HenryLi-0/raven/updatelogs/logs202507/07092025.md

# 7/9/2025 - 15th Update!

wow today was quite the day, its already 10 PM..., anyways watched another movie today, time to start working! yeah so today in the doctors office i got bored while waiting and decided to research a couple of boost convertors (since the current MT3608 we have has a max amp of 2A, which is quite sad when we want to power motors). anyways, found [this one](https://www.aliexpress.us/item/3256805882203198.html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), but it requires an input voltage of 10-32V, which the battery doesnt exactly deliver. therefore, we continue hunting.

yeah so its been 22 minutes and im starting to think there arent any boost convertors around for this job. so uh, found [this](https://www.aliexpress.us/item/2255800011462620.html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) but its limited to 5A in its input, so yeah. im kinda getting desperate here.

ok who keeps breaking the internet router

so i just had an idea, yeah its not gonna work (it was to skip the boost convertor for the motor and just attach it raw, but we need more volts!) yeah its been 45 minutes now and i cant find a good one. ok its now 11:05 PM and im just gonna take a break, ive looked through way too many aliexpress offers today...

ok im back at 12:15 AM and im honestly very tired lol, but lets try to push through.

[here's](https://www.aliexpress.us/item/3256805855172022.html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) a thing for 2A battery protection (choose `2S 20A Balance` or something)

alright, lets just finish this research phase, im getting really tired

what did i just come across

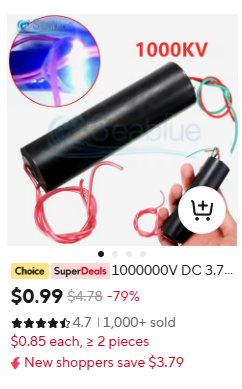
[picture p69: updatelogs/images/202507/07092025 - 1.png]
what this


ok theres actually no way i spent the entirety of today search for a single boost converter. anyways, im just gonna draw a wiring diagram real quick (yes for v3)

yeah so i just realized that... this soltuion kinda means that i need a step down to 5V thing for the motor system since we have a XIAO that doesnt want to become a frying pan

yeah ok, laid out all the components, its 1AM now, im just gonna wrap this up tomorrow (yay dont have to go outside tomorrow since its online on thursdays) (probably going to school on friday for driver practice? probably a good idea)

so yeah, thats it, good night!
