HenryLi-0/raven/updatelogs/logs202507/07062025.md

# 7/6/2025 - 12th Update!

yeah so we kinda gotta finish this...

just did a little research on the reviews of yesterday's overdischarge stuff, and it seems good! only downside is that its a *little* expensive (dont worry, welcome deal here! not sure how many deals i can get...) so, i guess we need to redraw the wiring diagram! (its 9:30 PM right now) wait a second, why does it say supply voltage 12V to 36V, guess this isnt the product for that!

so we need the entire battery output, but overdischarge protection to stop lower battery sus activity, so the battery should be able to deliver its stated 20A, but not get restrictied by the TP4056's 1A dishcharge thing (which is also one reason we arent including it on the spining bit now)

ok i gotta go for a second (its 10 right now), since my cousin is currently doing something in texas (i have no clue whats going on) ok three minutes later, and i guess they just diappeared off the face of the earth? i dont really know, gonna go back to search on aliexpress and LCSC, oh looks like theyre back

also the MT3608 that we had earlier does 2A max, which isnt enough... however, heres a [battery charger protection thing](https://www.aliexpress.us/item/3256807120302984.html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) (choose 2S 20A Balanced)! (uh idk if running this on only one battery would work?) yeah idk if this is the move, its layout looks super cursed, and im not exactly sure buying 4 batteries is the move. looking into making my own overdischarge protection circuit (bad idea), and i see a minecraft comparator reference

theres no way im soldering that

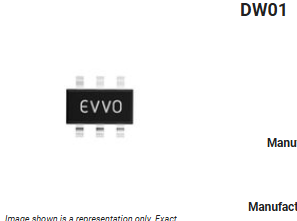
[picture p73: updatelogs/images/202507/07062025 - 1.png]
what the


anyways, heres some things i found:
- [1S 24A, might be the one! little sus, but should be good](https://www.aliexpress.us/item/3256805852468677.html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)
- [1S 10A, ok, less sus, but not enough amps!](https://www.aliexpress.us/item/3256806617397129.html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)
- [some 18650 format battery holder of sorts](https://www.digikey.com/en/products/detail/keystone-electronics/1044/5057795)

ok anyways its 11PM and im off to watch frozen 2 for like the fifteenth time ok see ya

ok its 12:13 AM and i just finished reading all the FRC servers im in (lurking behavior), anyways back to aliexpress! the `1S 24A` one (the first link) seems pretty ok, a little sketchy (not too many reviews) and one picture has a chip without a part marking in the photo, but reviews seem alright and the pictures. also, just realized, these will take a LONG time to ship. like it says july 19-22. eh, i guess trade off for being so cheap.

ok, so thats good! time to hunt LCSC for an A3144 and the MOSFET

hmm you need to by 5 A3144 at once, but i guess LCSC is better since its like $4 on aliexpress for also 5 (also, LCSC is probably more reputable) [here's](https://lcsc.com/product-detail/Hall-Switches_JSMSEMI-A3144EUA-T-JSM_C18188954.html?s_z=n_a3144) the link! also, whys the datasheet only in chinese

also, AP scores dont appear out yet? guess ill check in the morning

ok, since the pdf didnt allow copy pasting, i just downloaded it, went to google drive, uploaded it, and now i can copy and paste. yeah it just works like that. anyways, looks good! gonna hunt for the mosfet now, we also need leds...

yep, [here's](https://lcsc.com/product-detail/MOSFETs_STMicroelectronics-STP55NF06L_C77582.html?s_z=n_STP55NF06L) the STP55NF06L, cheaper than digikey!

ok, WS2812B now, shouldnt be too hard... oh yeah, nvm, since theres apparently 46 different ones, guess i spoke too soon... also thats crazy, 983885 and 1010610 leds in stock, how many do they mass produce at once?

waa who makes this many leds? (please send me your secret led stash)

leds leds leds

wait i need to find what footprint or at least what the LEDs i have look like... ok, whatever `LED_WS2812B_PLCC4_5.0x5.0mm_P3.2mm` means (probably 5mm by 5mm base and 3.2mm tall?) reading through [this datasheet](https://lcsc.com/datasheet/lcsc_datasheet_2506031657_XINGLIGHT-XL-5050RGBC-WS2812B_C2843785.pdf) for [these leds](https://lcsc.com/product-detail/RGB-LEDs-Built-in-IC_XINGLIGHT-XL-5050RGBC-WS2812B_C2843785.html?s_z=n_ws2812b) and dont really get whats 500 euros?

wha

wait this is funny

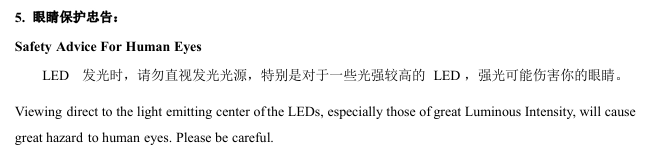
[picture p74: updatelogs/images/202507/07062025 - 4.png]
oops


anyways, im gonna continue research on the phone, currently 1:02 AM! (lots of things start tomorrow, guess i should try sleeping earlier today? probably not)
