HenryLi-0/raven/updatelogs/logs202506/06302025.md

# 6/30/2025 - 6th Update!

ok, nearing a week soon! today's CAD day! or more like tomorrow, since its actually 2 AM on 6/30/2025, and i just pushed the commit with the 6/29/2025 log (im a little too excited to work on this)

but since that's cad day, im actually gonna work on some of the firmware now! ok so its 2:37 AM now, and i got the theoretical settings and startup done, so now all the logic (predictive RPM and timing) needs to be done. gotta search this up, but hopefully it has decimal time tracking (as in, `time.time()` returns a decimal), since if it only returned whole numbers, that would make things a little less accurate!

ok, good night, see you tomorrow morning! (cad cad cad)

ok its 4:07 PM now, time to start CADing! gonna quickly export the kicad files into stl...

ok, everything imported (except that motor... do i just go hunting on aliexpress again?), lets get the CAD started! (its 4:25 PM now!) i guess we do a mastersketch (*DDS noises* (FRC reference))

ok so we need something heavy to keep the whole thing down ~~and not take off~~, so i guess we just make the top as light as possible (pocketing time) and the bottom have attachemts to put something like a weight on (or just make it heavy in general)

also turns out im actually designed it for M4 screws??? ok, wait, let me just take a break and think about this, since this CAD is not going the way i want it. what we want is a setup that looks like this:

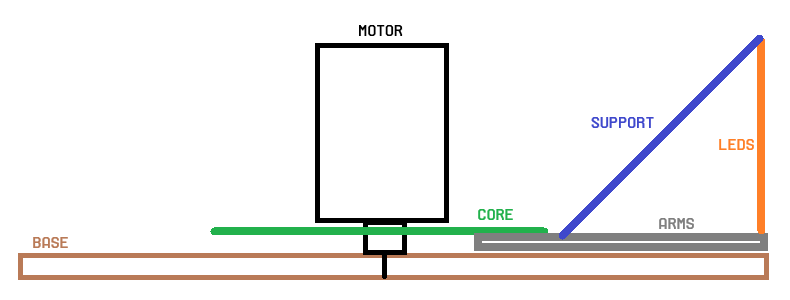
[picture p87: updatelogs/images/202506/06302025 - 1.png]
ms paint


and top down, something like (ok left at 5:05 PM and back at 11:20 PM!) (so uh kinda 6 hours passed and oopsie)

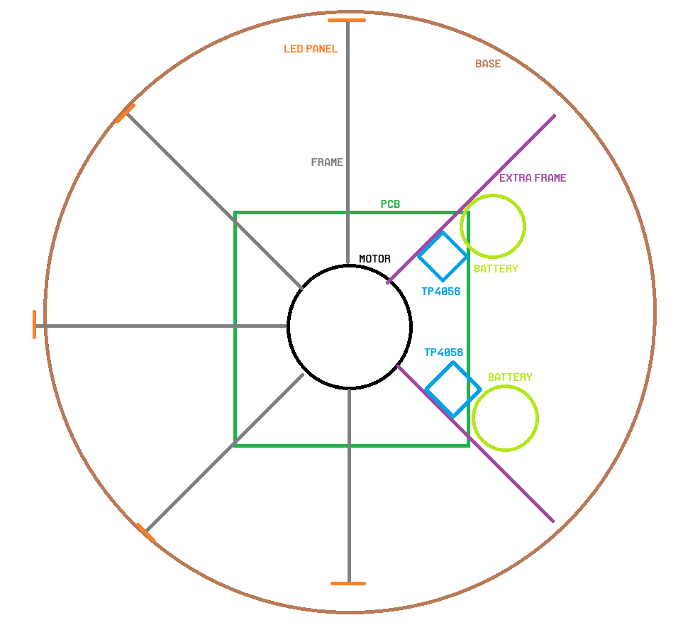
[picture p88: updatelogs/images/202506/06302025 - 2.png]
ms paint again


ignoring the fact that they are very not to scale, that's the general idea we're going for! gonna quickly take a visit to the bathroom, then we continue the CAD!

ok i need to figure out what motor im using, since i dont think using amazon shipping is gonna give the best prices (but, i really need to be careful of getting scammed on aliexpress lol) (mfw i say that and the second option is 3 motors prices at $0.99)

ok, so we need a shaft that isnt a perfect cylinder, or else we will not be able to get a grip... ok, so i actually cant find any non-sketchy D-shaft 775 motor, so i guess im gonna use [this one](https://www.aliexpress.us/item/3256807114067845.html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) that has a circular shaft, so ill probably use some hub or something (or just use superglue? idk)

hey, add [M4 screws (M4, 20mm)](https://www.aliexpress.us/item/3256804341271555.html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) to the BOM! and [these brass heat inserts (M4, OD 6mm, length 5mm)](https://www.aliexpress.us/item/3256803396040989.html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) while youre at it! and [these M4 nuts (M4)](https://www.aliexpress.us/item/3256807407546447.html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)! (ill have to look into this, but i *could* use the heat inserts as nuts... might be a bad idea, but ill look into it)

ok, gotta go to sleep now (its so early), but i do have a meeting tomorrow that i'll definitely not use to work on the CAD... no no, that would be such a terrible idea... who would ever do such thing? (*subtle foreshadowing*)

ok, just realized that the motor has some threaded m4 holes already! gotta update the PCB now, but heres the CAD so far!

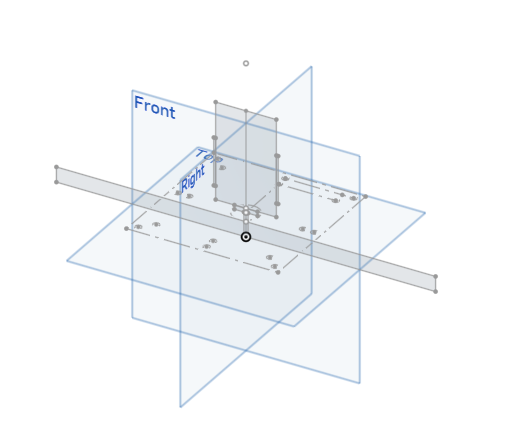
[picture p89: updatelogs/images/202506/06302025 - 3.png]
cad


ok good night now! (oops got caught being up at 12:40 AM oops)
