HenryLi-0/raven/updatelogs/logs202506/06262025.md

# 6/26/2025 - 2nd Update!

ok, so we're back! so, did a couple tests today...

**Test 1!**

firstly (sorry, this first one has no pictures), how fast do the LEDs have to flash before I can't see them changing? Turns out, around a wait time of `0.01` seconds was roughly the point where the colors seemed to start to seamlessly merge! Here's the example code:

```
import board
import neopixel
import time

led = board.D6
pixels = neopixel.NeoPixel(led, 9)
buffer = lambda ie: [ie for i in range(9)]

t = 0
while True:
    pixels[:] = buffer((255,0,0)) if t % 2 == 0 else buffer((0,0,255))
    t += 1
    time.sleep(0.01)
```

and after tuning the last line, we start to see purple! of course, the LEDs are still flashing the correct colors, as can be told by the fact that they are always red or blue when it "pauses" when you save firmware onto it. this means that, neopixels can, in fact, blend colors through pulsing colors faster than human detection! of course, we can't exactly test how fast they can update, but i do have an idea for later.

**Test 2!**

but now, a problem seems apparent. since we're spinning it round and round, for a certain period of time, one side does not recieve any light. basically, it acts sort of like PWM (you know, pulse width modulation), a strategy where "flickering" a device (such as an LED) is used to safely create an effect of percentage (so a half bright LED is powered 50% of the time). search it up, it'll explain better!

simply, we have to look at the effects of reduced light on the total brightness! of course, there is obviously an effect, but here's a comparison (LED flickering at max speed)

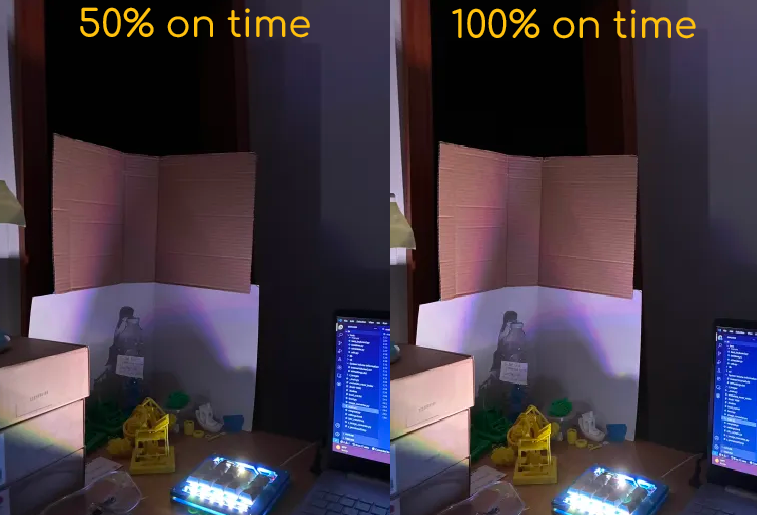
[picture p94: updatelogs/images/202506/06262025 - 1.png]
waw


no difference? try looking at the top right of each photo! the camera seems to catch the right photo with a bit more light! simply, the effect in person wasn't too much, it was noticably dimmer, but this shouldnt be an issue once we have nearly x5 the LEDs we currently have (49 outwards LEDs is crazy!)

and yeah, so interesting tests today! i'll be pretty busy tomorrow, but the plan is to find specifics (motor power, good motor speeds, battery stuff, etc.)! also, yes, i used my hackpad for this! ok, that's all for today, good night!
