HenryLi-0/raven/updatelogs/logs202508/08062025.md

# 8/6/2025 - 40th Update!

dealing 4 repositories of work at once isnt a good idea is it...

welcome back! todays just another quick update on the arrivals of stuff! today, LCSC packages came, two in fact! one containing a bunch of neat electronics, the other also containing neat electronics, except just one of them, that being the MOSFET! anyways, other than that, aliexpress has just told me that the package is now "at the local delivery center" and is about to take its final stretch to get here! luckily for me, i just happen to be able to stay home for the entirety of tomorrow!

at this very moment, in a repository far from here, a new repository rises to another YSWS! yep, planning on doing this one in 10 days, which is kinda insane. anyways, if we pull this off, it would be quite nice, except for the fact it kinda messes with my entire summer schedule. yeah, sorry ivo, gotta wait like two weeks...

anyways, thats about it! its just aliexpress and the PCBs, and we can get working! speaking of which, a quick update on JLCPCB, the package has also arrived at the same distribution facility, just one day shy of the LCSC ones! this means, hopefully, that it might come... tomorrow? we'll see! but for now, we wait for the local carrier on their way!

that's it folks! ok, yeah, got everything laid out on the table, hopefully we can begin assembly friday or this weekend! ok, good night!
