HenryLi-0/raven/PCB/repo.png

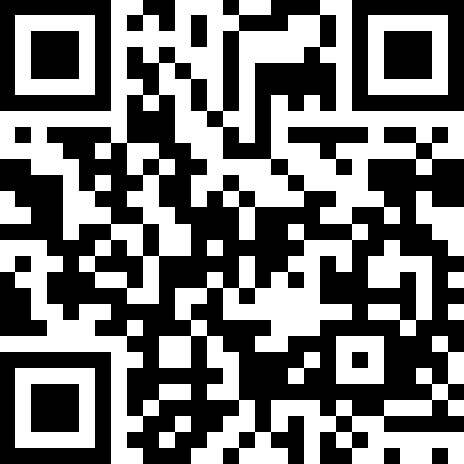
PCB/repo.png
