HenryLi-0/raven/PCB/vanity.png

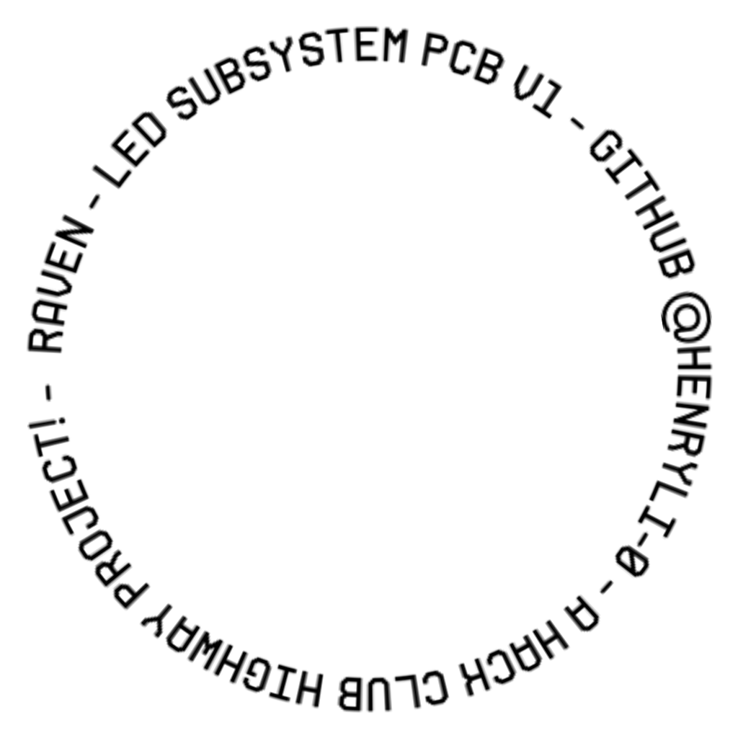
PCB/vanity.png
