HenryLi-0/raven/printing/motor top mount.step

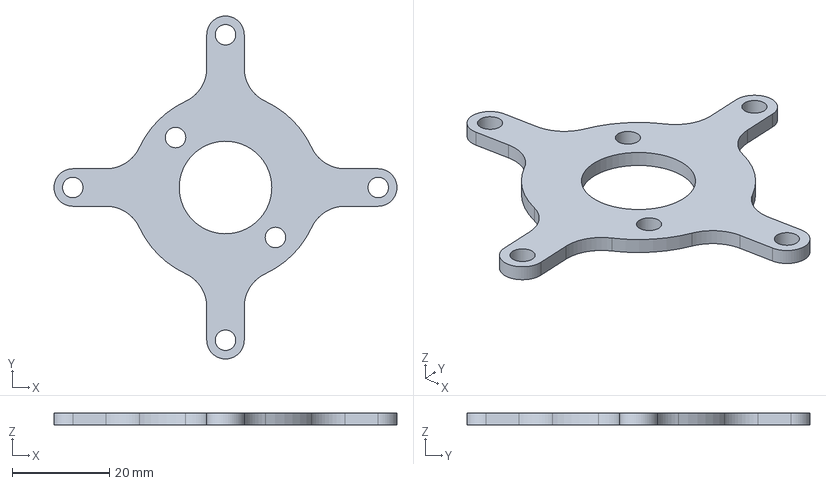
[picture p112: CAD file, 2025-08-12]
printing/motor top mount.step
70.4 x 70.4 x 2.50 mm
