HenryLi-0/raven/CAD/Arms/Raven-arm (diagonal)-2025-07-26 00-59-21.step

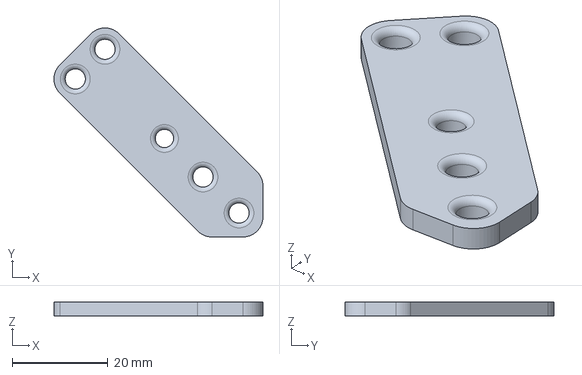
[picture p113: CAD file, 2025-07-26]
CAD/Arms/Raven-arm (diagonal)-2025-07-26 00-59-21.step
43.6 x 43.6 x 3.00 mm
