HenryLi-0/raven/CAD/Bracket/Raven-bracket ring-2025-07-26 00-59-33.step

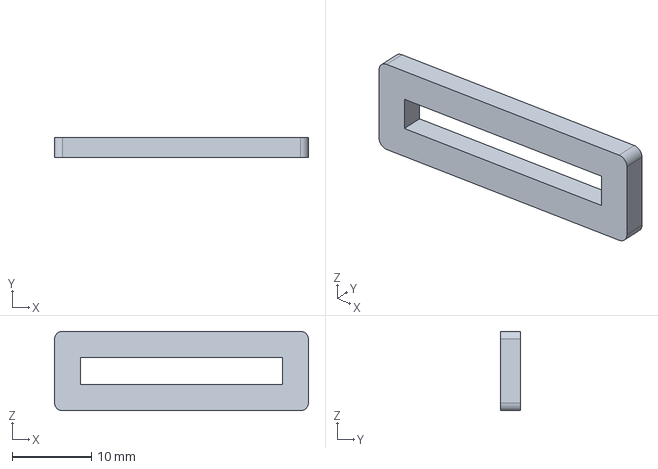
[picture p114: CAD file, 2025-07-26]
CAD/Bracket/Raven-bracket ring-2025-07-26 00-59-33.step
32.0 x 2.50 x 10.00 mm
