HenryLi-0/raven/CAD/Middle bits/Raven-motor top mount-2025-07-26 01-00-28.step

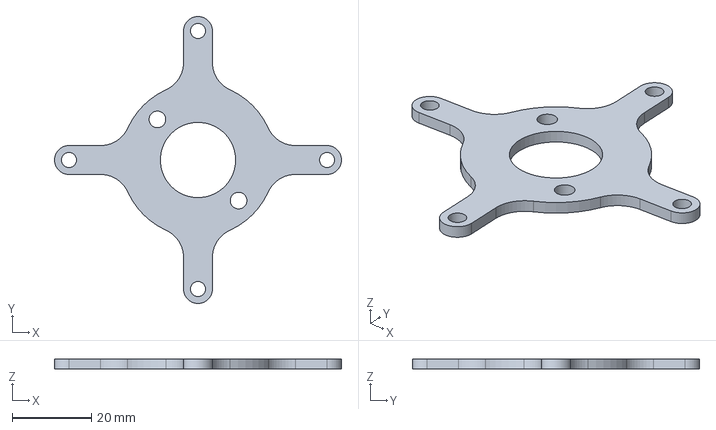
[picture p115: CAD file, 2025-07-26]
CAD/Middle bits/Raven-motor top mount-2025-07-26 01-00-28.step
72.5 x 72.5 x 2.50 mm
