HenryLi-0/raven/CAD/Motor bottom support/Raven-motor bottom mount-2025-07-26 01-00-34.step

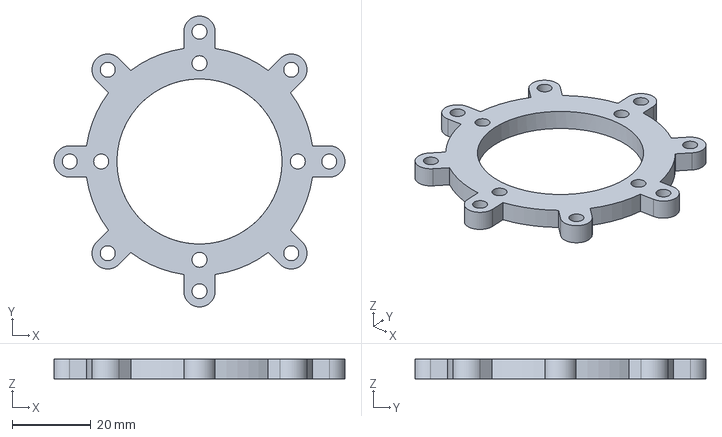
[picture p116: CAD file, 2025-07-26]
CAD/Motor bottom support/Raven-motor bottom mount-2025-07-26 01-00-34.step
74.0 x 74.0 x 5.00 mm
