HenryLi-0/raven/CAD/PCB representations/Raven-motor pcb-2025-07-26 01-02-24.step

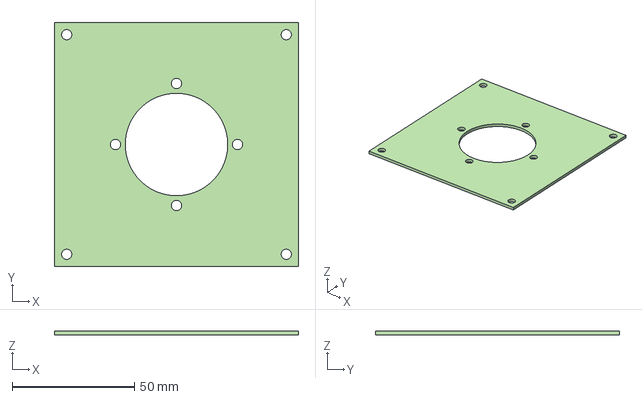
[picture p117: CAD file, 2025-07-26]
CAD/PCB representations/Raven-motor pcb-2025-07-26 01-02-24.step
100.0 x 100.0 x 1.60 mm
