HenryLi-0/raven/printing/3mf/electronics cover spacer x4.3mf

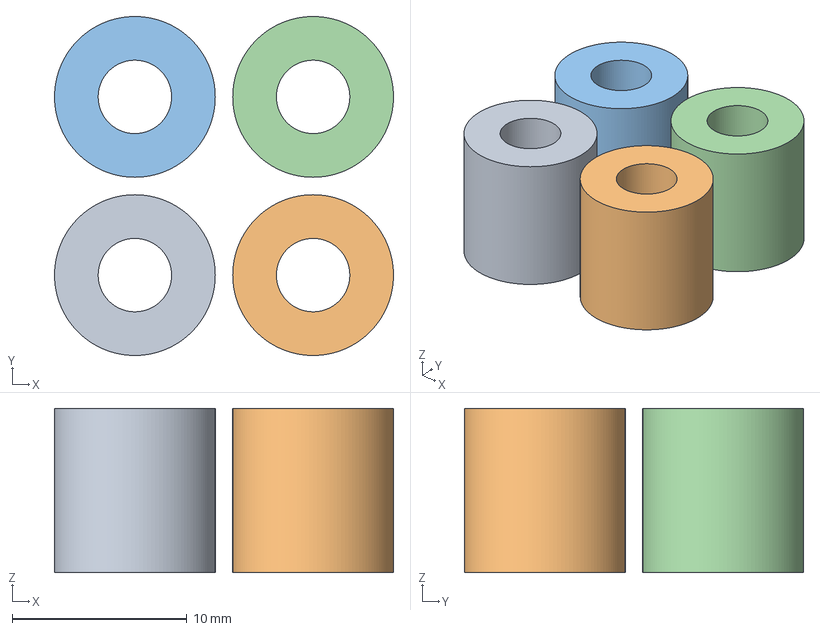
[picture p118: CAD file, 2025-08-08]
printing/3mf/electronics cover spacer x4.3mf
19.4 x 19.4 x 9.40 mm
electronics cover spacer.step x 4
