HenryLi-0/raven/CAD/Arms/Raven-inner spacer-2025-07-26 00-59-55.step

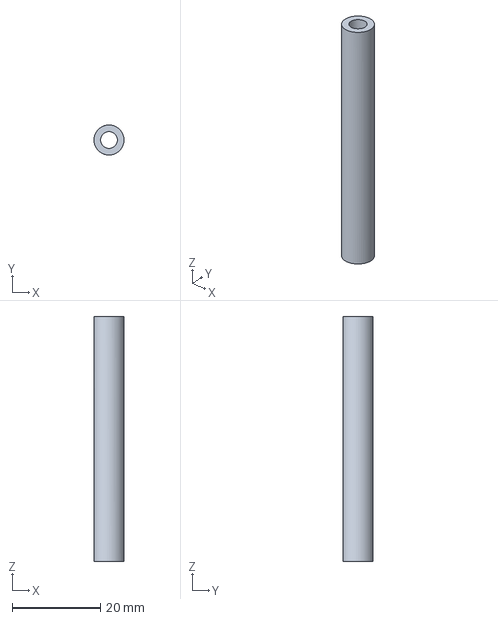
[picture p119: CAD file, 2025-07-26]
CAD/Arms/Raven-inner spacer-2025-07-26 00-59-55.step
6.80 x 6.80 x 55.4 mm
