HenryLi-0/raven/CAD/Bracket/Raven-bracket bracket-2025-07-26 00-59-29.step

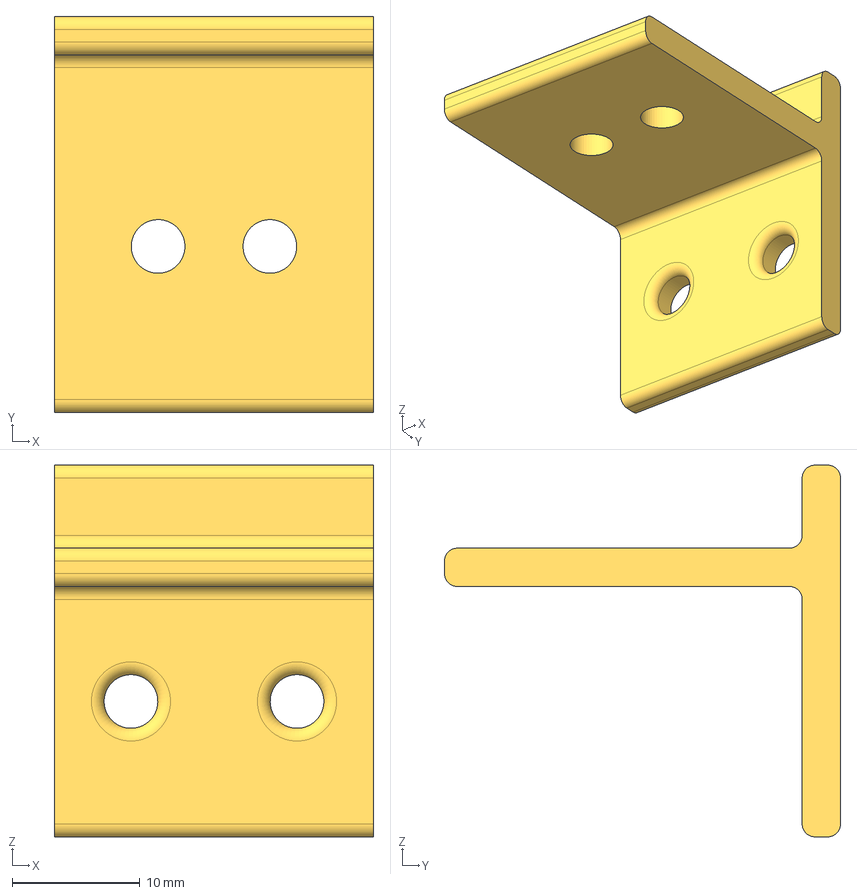
[picture p120: CAD file, 2025-07-26]
CAD/Bracket/Raven-bracket bracket-2025-07-26 00-59-29.step
25.0 x 31.0 x 29.1 mm
