HenryLi-0/raven/CAD/Motor bottom support/Raven-support leg straight-2025-07-26 01-00-44.step

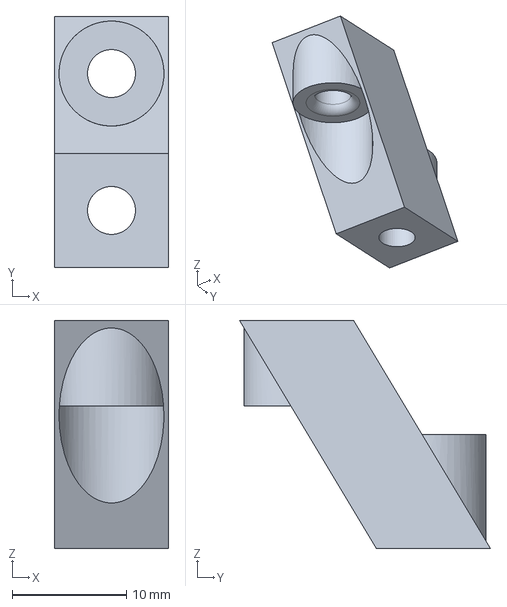
[picture p121: CAD file, 2025-07-26]
CAD/Motor bottom support/Raven-support leg straight-2025-07-26 01-00-44.step
10.0 x 22.0 x 20.0 mm
