HenryLi-0/raven/CAD/PCB representations/Raven-led panel-2025-07-26 01-02-17.step

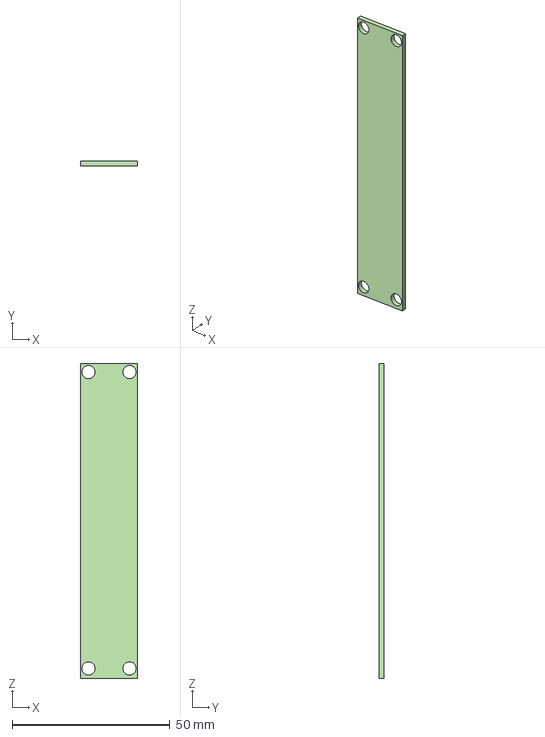
[picture p122: CAD file, 2025-07-26]
CAD/PCB representations/Raven-led panel-2025-07-26 01-02-17.step
18.0 x 1.60 x 99.9 mm
