HenryLi-0/raven/printing/3mf/support leg spacer x4.3mf

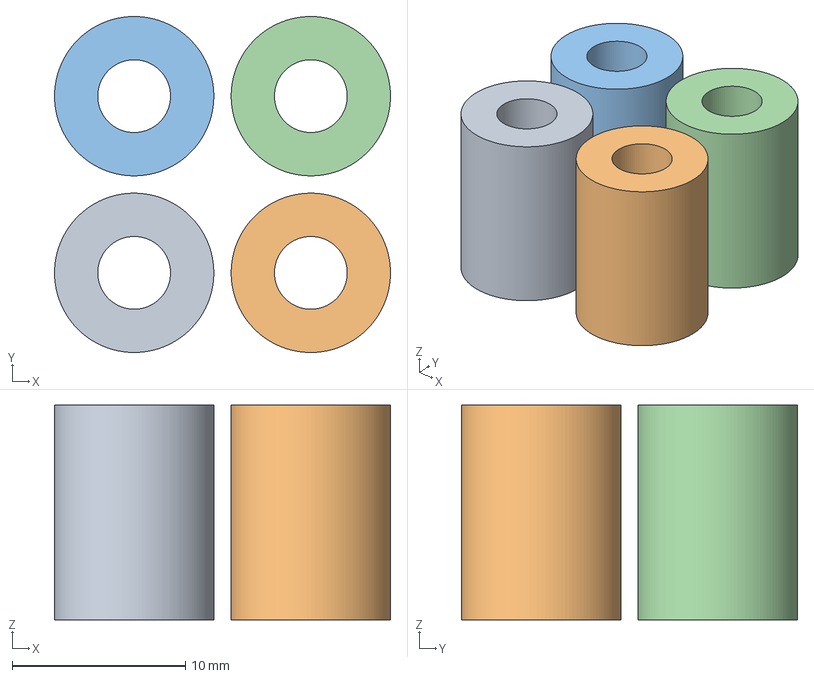
[picture p123: CAD file, 2025-08-08]
printing/3mf/support leg spacer x4.3mf
19.4 x 19.4 x 12.4 mm
support leg spacer.step x 4
