HenryLi-0/raven/printing/support leg spacer.step

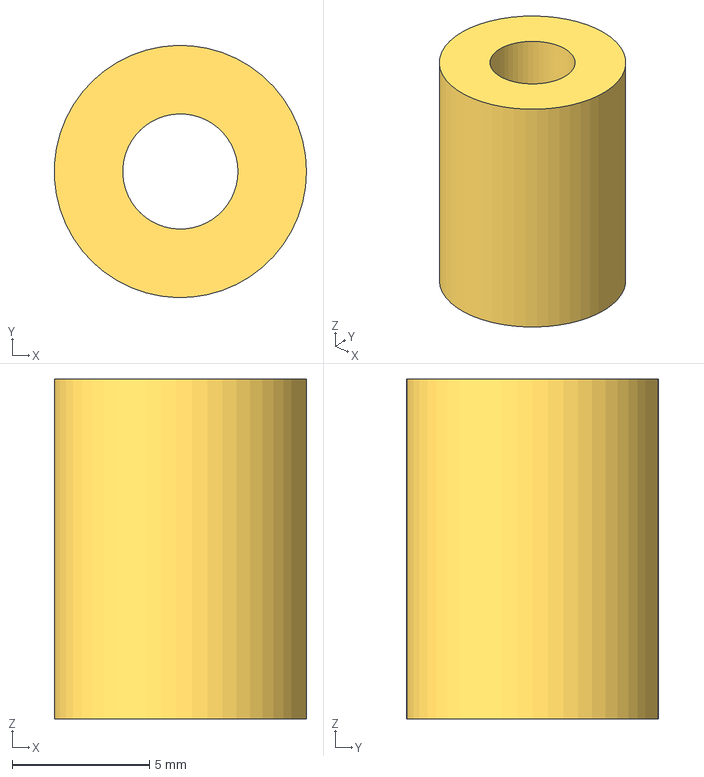
[picture p124: CAD file, 2025-08-08]
printing/support leg spacer.step
9.19 x 9.20 x 12.4 mm
