HenryLi-0/raven/CAD/Arms/Raven-arm (straight)-2025-07-26 00-59-16.step

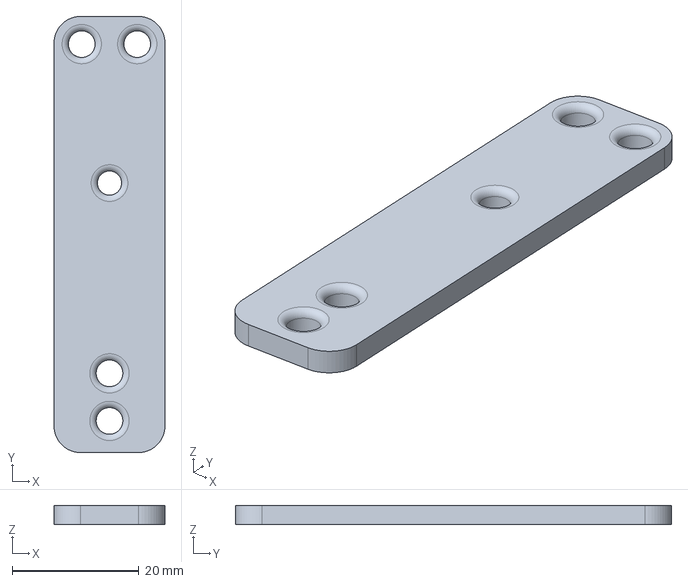
[picture p125: CAD file, 2025-07-26]
CAD/Arms/Raven-arm (straight)-2025-07-26 00-59-16.step
17.5 x 68.8 x 3.00 mm
