HenryLi-0/raven/CAD/Motor bottom support/Raven-motor bottom spacer-2025-07-26 01-00-40.step

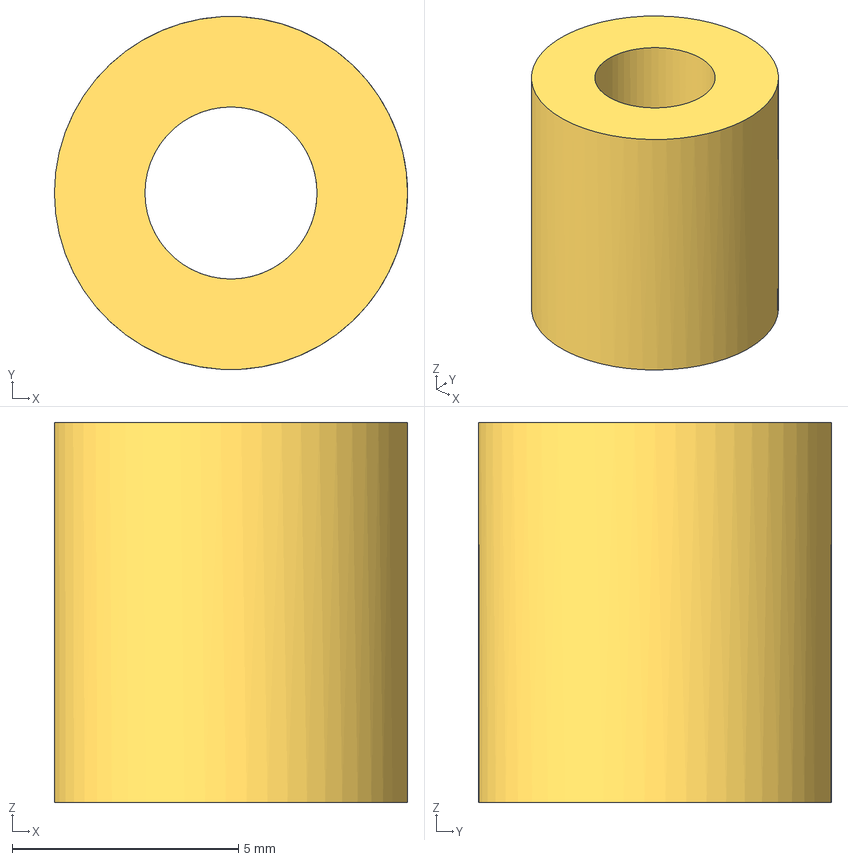
[picture p126: CAD file, 2025-07-26]
CAD/Motor bottom support/Raven-motor bottom spacer-2025-07-26 01-00-40.step
7.80 x 7.80 x 8.40 mm
