HenryLi-0/raven/printing/3mf/electronics cover x1.3mf

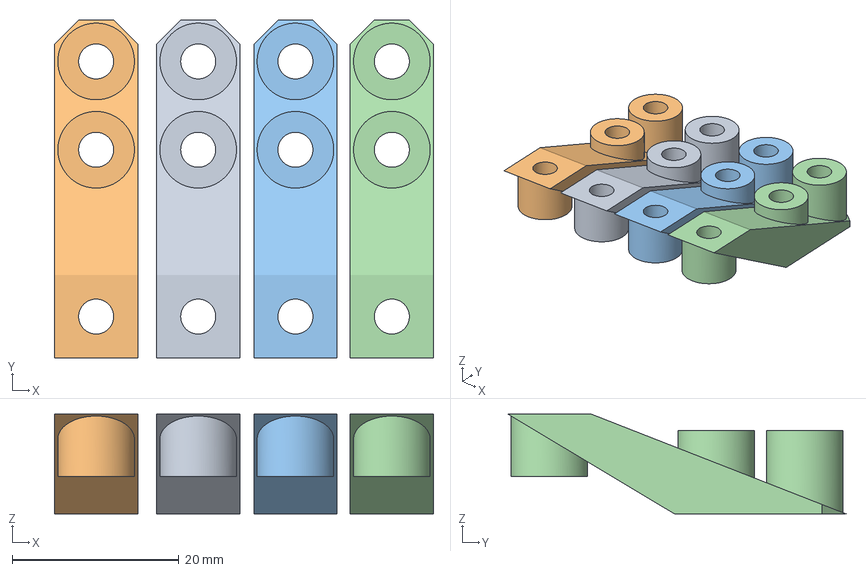
[picture p127: CAD file, 2025-08-08]
printing/3mf/electronics cover x1.3mf
45.5 x 40.6 x 12.0 mm
support leg diagonal.step x 4
