HenryLi-0/raven/printing/alignment disc.step

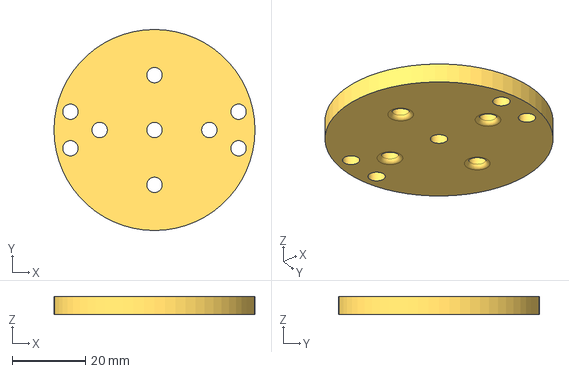
[picture p128: CAD file, 2025-08-08]
printing/alignment disc.step
55.0 x 55.0 x 5.00 mm
