HenryLi-0/raven/printing/electronics cover spacer.step

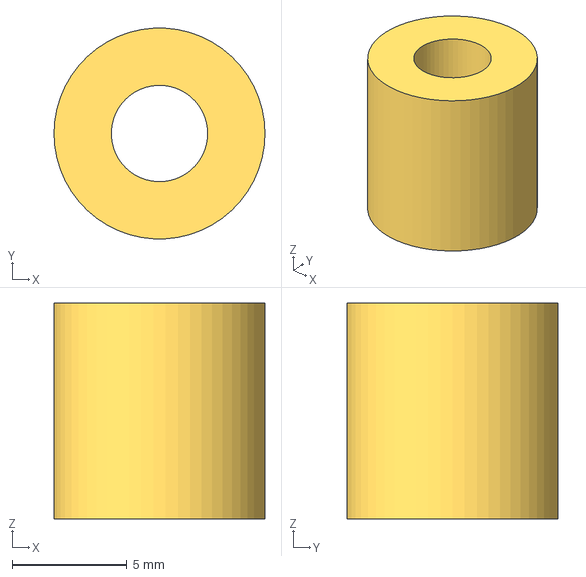
[picture p129: CAD file, 2025-08-08]
printing/electronics cover spacer.step
9.20 x 9.18 x 9.40 mm
