HenryLi-0/raven/printing/3mf/shaft collar (both).3mf

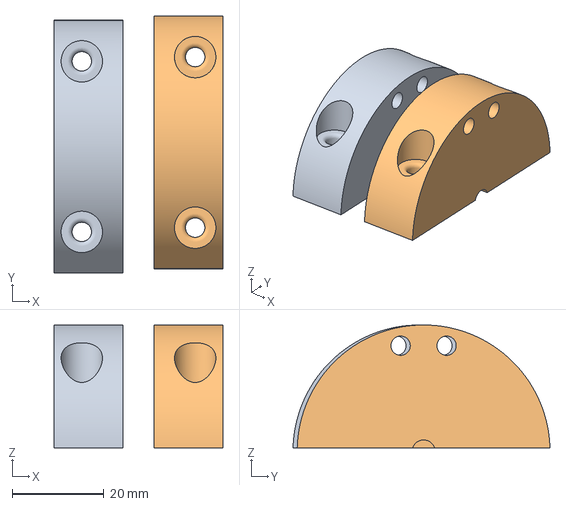
[picture p130: CAD file, 2025-08-08]
printing/3mf/shaft collar (both).3mf
36.7 x 55.9 x 26.8 mm
left shaft collar.step
right shaft collar.step
