HenryLi-0/raven/printing/3mf/support leg diagonal x4.3mf

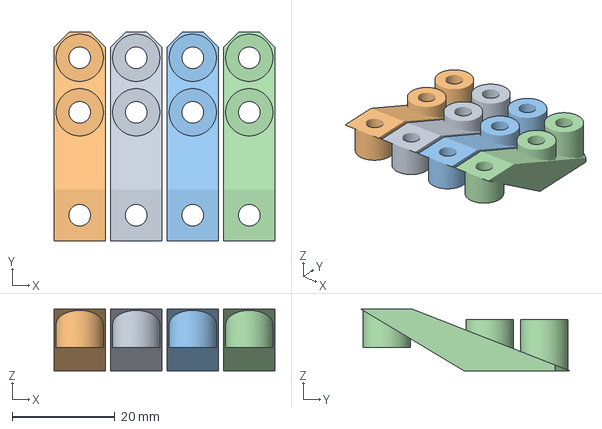
[picture p131: CAD file, 2025-08-08]
printing/3mf/support leg diagonal x4.3mf
43.0 x 40.6 x 12.0 mm
support leg diagonal.step x 4
