HenryLi-0/raven/printing/support leg straight.step

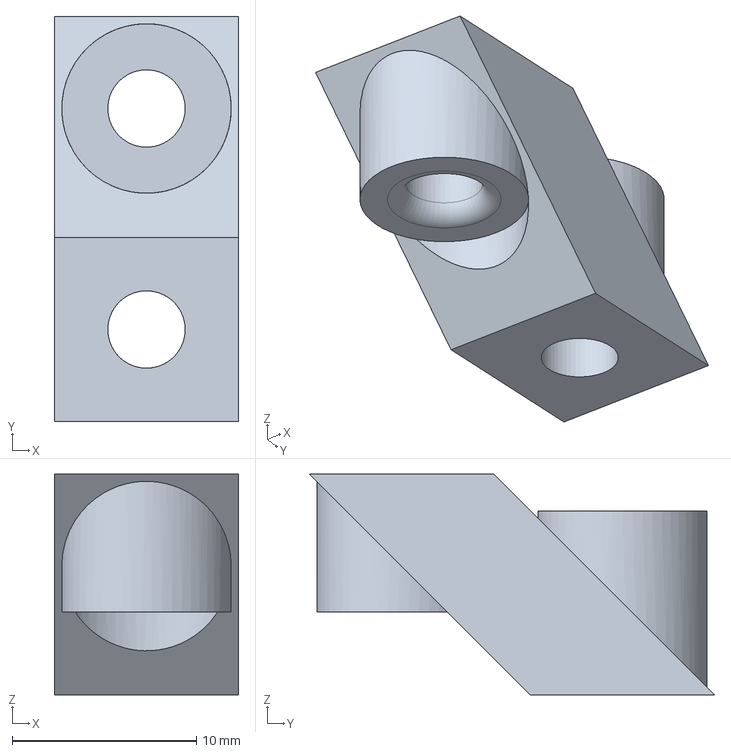
[picture p132: CAD file, 2025-08-08]
printing/support leg straight.step
10.0 x 22.0 x 12.0 mm
