HenryLi-0/raven/printing/3mf/support leg straight x4.3mf

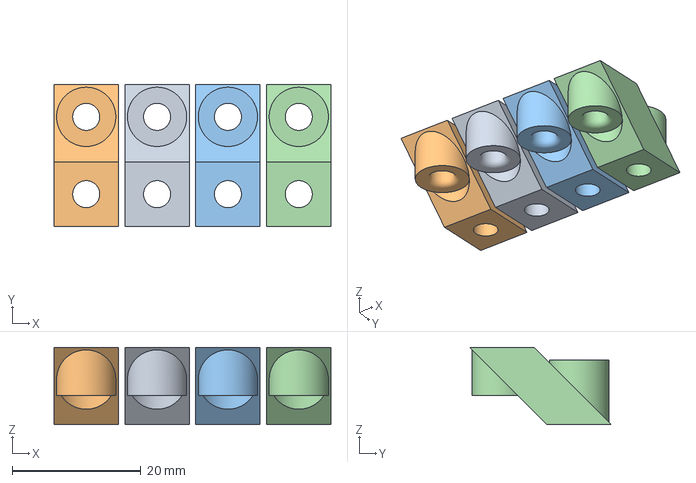
[picture p133: CAD file, 2025-08-08]
printing/3mf/support leg straight x4.3mf
43.0 x 22.0 x 12.0 mm
support leg straight.step x 4
