HenryLi-0/raven/printing/left shaft collar.step

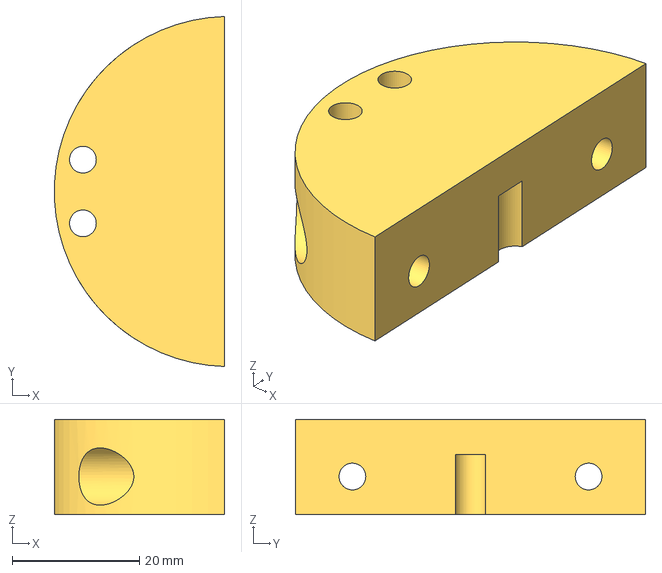
[picture p134: CAD file, 2025-08-08]
printing/left shaft collar.step
26.7 x 55.0 x 15.0 mm
