HenryLi-0/raven/printing/3mf/bracket arm spacer x5.3mf

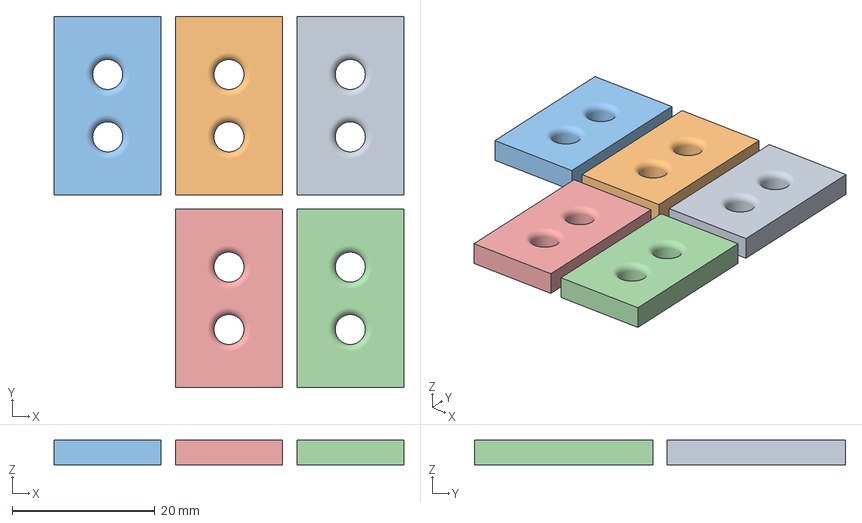
[picture p135: CAD file, 2025-07-31]
printing/3mf/bracket arm spacer x5.3mf
49.0 x 52.0 x 3.50 mm
bracket arm spacer.step x 5
