HenryLi-0/raven/printing/support leg diagonal.step

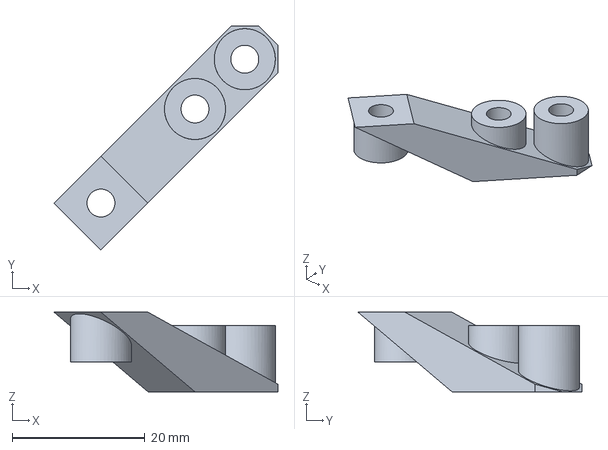
[picture p136: CAD file, 2025-08-08]
printing/support leg diagonal.step
33.7 x 33.7 x 12.0 mm
