HenryLi-0/raven/printing/3mf/outer spacer x4.3mf

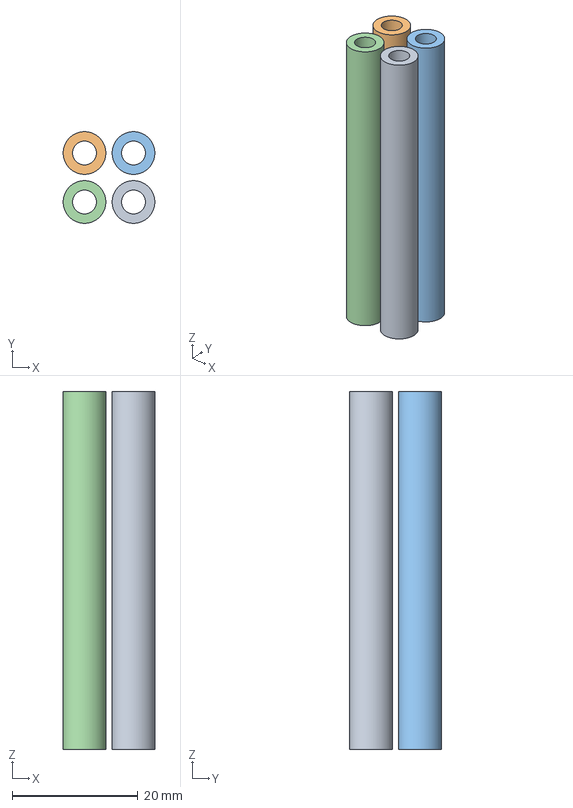
[picture p137: CAD file, 2025-07-31]
printing/3mf/outer spacer x4.3mf
14.6 x 14.6 x 57.0 mm
outer spacer.step x 4
