HenryLi-0/raven/printing/electronics cover.step

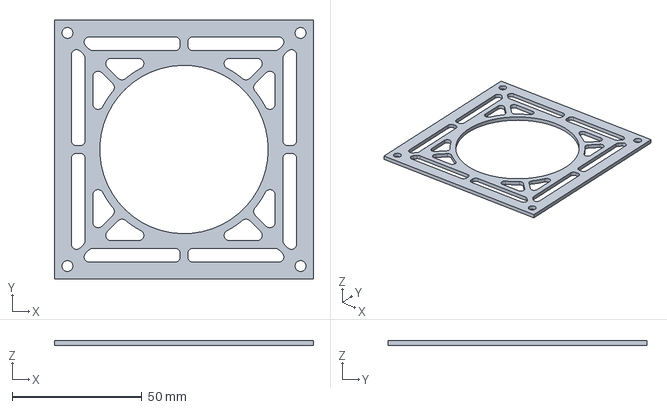
[picture p138: CAD file, 2025-08-08]
printing/electronics cover.step
100.0 x 100.0 x 2.00 mm
