HenryLi-0/raven/printing/3mf/inner spacer x5.3mf

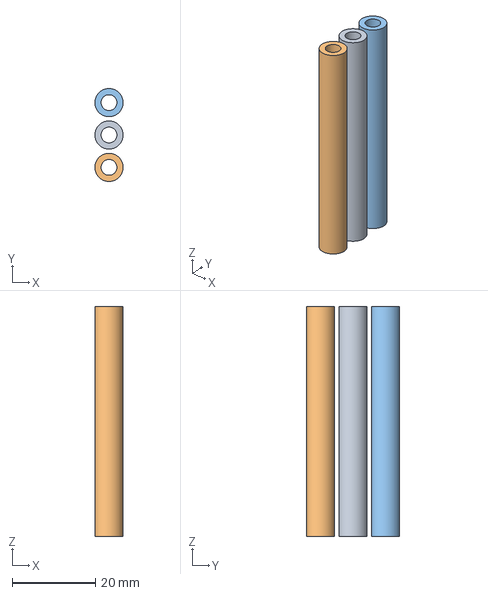
[picture p139: CAD file, 2025-07-31]
printing/3mf/inner spacer x5.3mf
6.80 x 22.4 x 55.4 mm
inner spacer.step x 3
