HenryLi-0/raven/printing/3mf/bracket led spacer x5.3mf

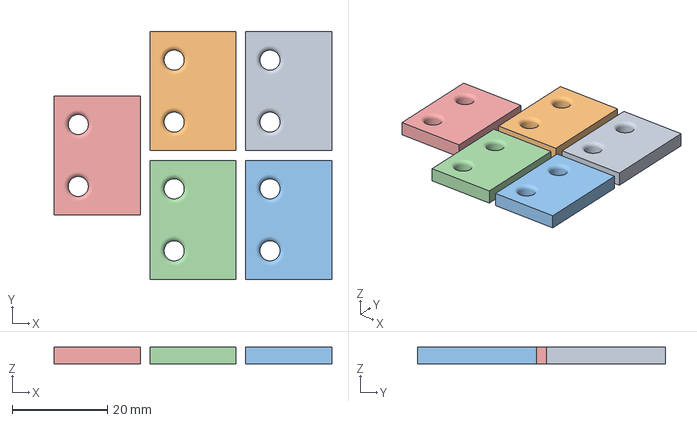
[picture p140: CAD file, 2025-07-31]
printing/3mf/bracket led spacer x5.3mf
58.3 x 52.0 x 3.50 mm
bracket led spacer.step x 5
