HenryLi-0/raven/printing/3mf/bracket ring x10.3mf

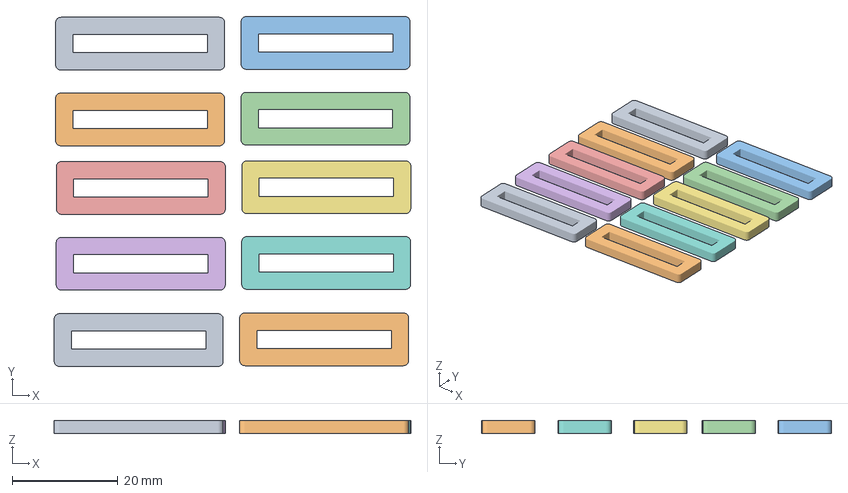
[picture p141: CAD file, 2025-07-31]
printing/3mf/bracket ring x10.3mf
67.5 x 66.2 x 2.50 mm
bracket ring.step x 10
