HenryLi-0/raven/printing/3mf/bracket bracket x2.3mf

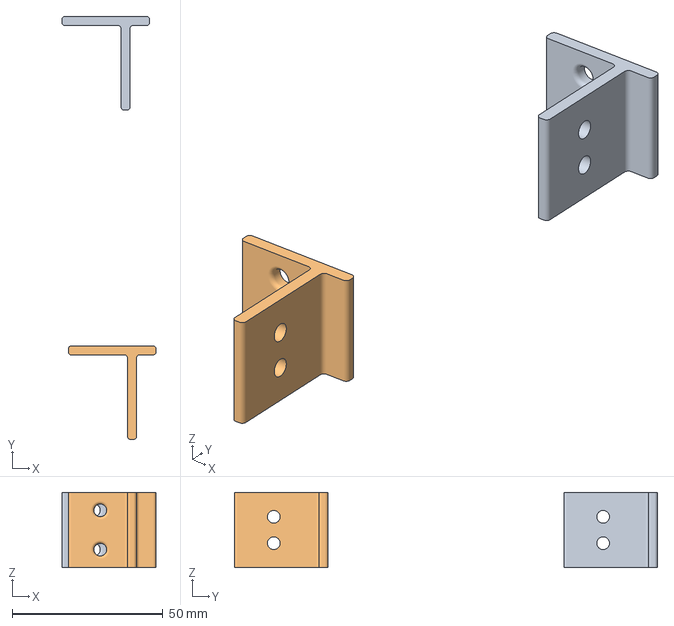
[picture p142: CAD file, 2025-07-30]
printing/3mf/bracket bracket x2.3mf
31.2 x 140.1 x 25.0 mm
bracket bracket.step x 2
