HenryLi-0/raven/printing/3mf/bracket bracket x4.3mf

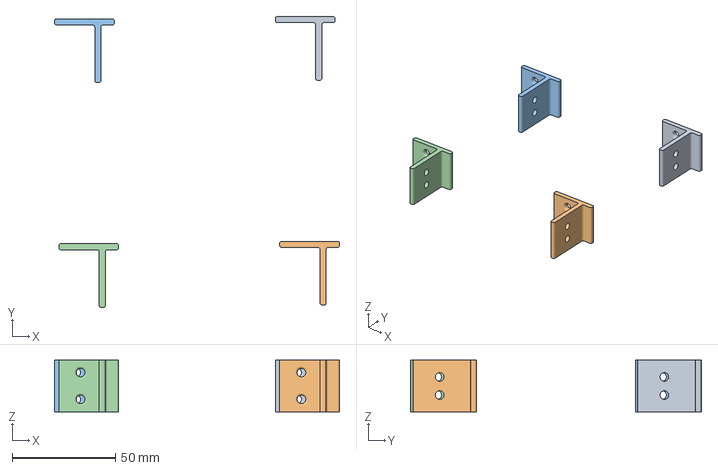
[picture p143: CAD file, 2025-07-30]
printing/3mf/bracket bracket x4.3mf
138.4 x 141.2 x 25.0 mm
bracket bracket.step x 4
