HenryLi-0/raven/printing/3mf/electronics attachment x2.3mf

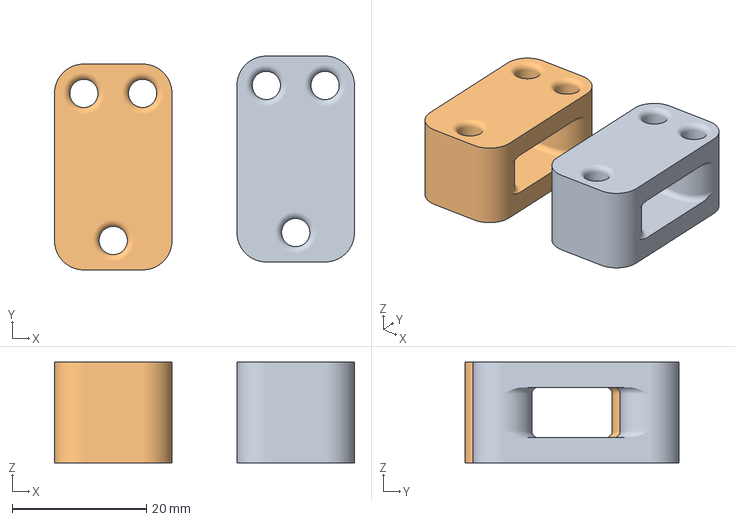
[picture p144: CAD file, 2025-07-30]
printing/3mf/electronics attachment x2.3mf
44.7 x 31.8 x 15.0 mm
electronics attachment.step x 2
