HenryLi-0/raven/firmware/led/subsystems/hall.py

import digitalio

from constants import *

class Hall:
    def __init__(self, pin):
        self.sensor = digitalio.DigitalInOut(pin)
        self.sensor.direction = digitalio.Direction.INPUT
    def getValue(self):
        # Returns the value of the Hall Effect Sensor.
        return self.sensor.value


HALL = Hall(Constants.PIN_HALL)
